afonsus1997/Pixels-Camp-PCB-Badge/Blog Writeup/Pictures/chargingcircuit.png

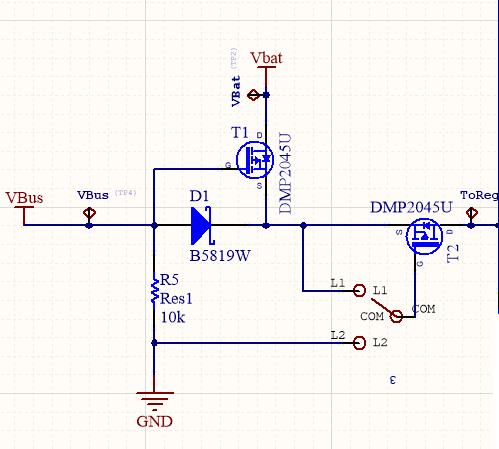
Blog Writeup/Pictures/chargingcircuit.png
