afonsus1997/Pixels-Camp-PCB-Badge/Blog Writeup/Pictures/chargingsilkscreen.PNG

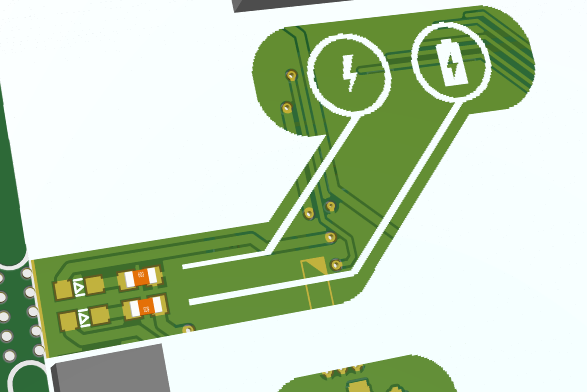
Blog Writeup/Pictures/chargingsilkscreen.PNG
