afonsus1997/Pixels-Camp-PCB-Badge/Blog Writeup/Pictures/devboard.jpg

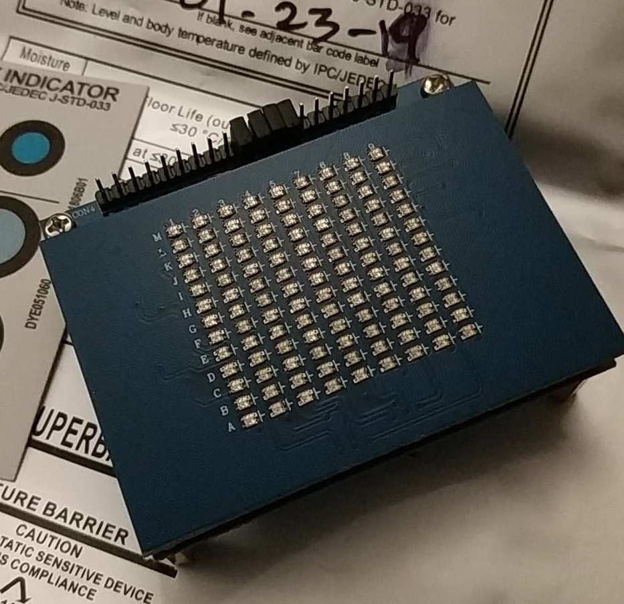
Blog Writeup/Pictures/devboard.jpg
