afonsus1997/Pixels-Camp-PCB-Badge/Blog Writeup/Pictures/DTRRST.PNG

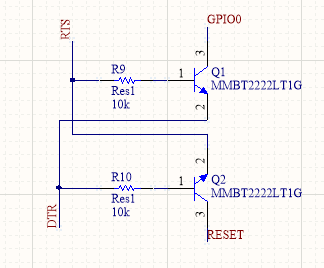
Blog Writeup/Pictures/DTRRST.PNG
