afonsus1997/Pixels-Camp-PCB-Badge/Blog Writeup/Pictures/esp32-wroom.jpg

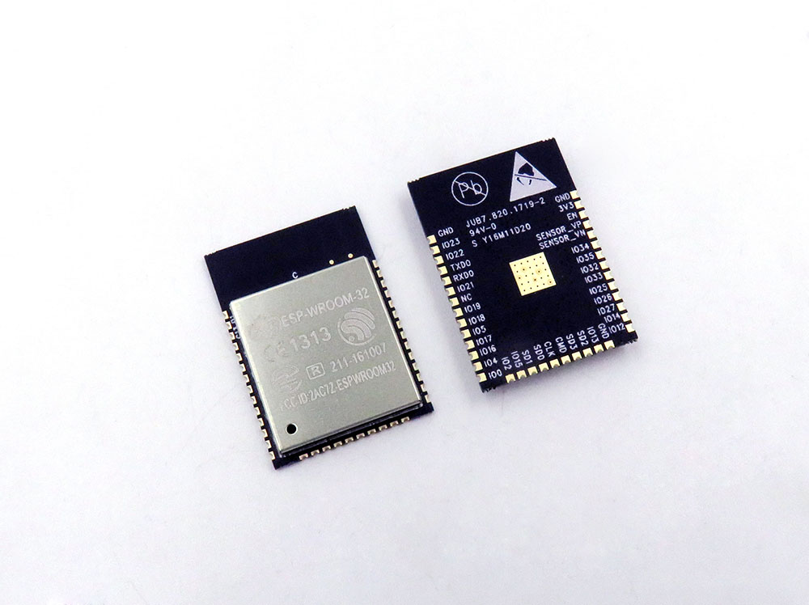
Blog Writeup/Pictures/esp32-wroom.jpg
