afonsus1997/Pixels-Camp-PCB-Badge/Blog Writeup/Pictures/esp32_pullup.PNG

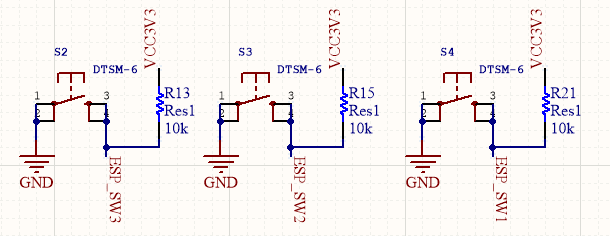
Blog Writeup/Pictures/esp32_pullup.PNG
