afonsus1997/Pixels-Camp-PCB-Badge/Blog Writeup/Pictures/Ledmatrix_pcb.PNG

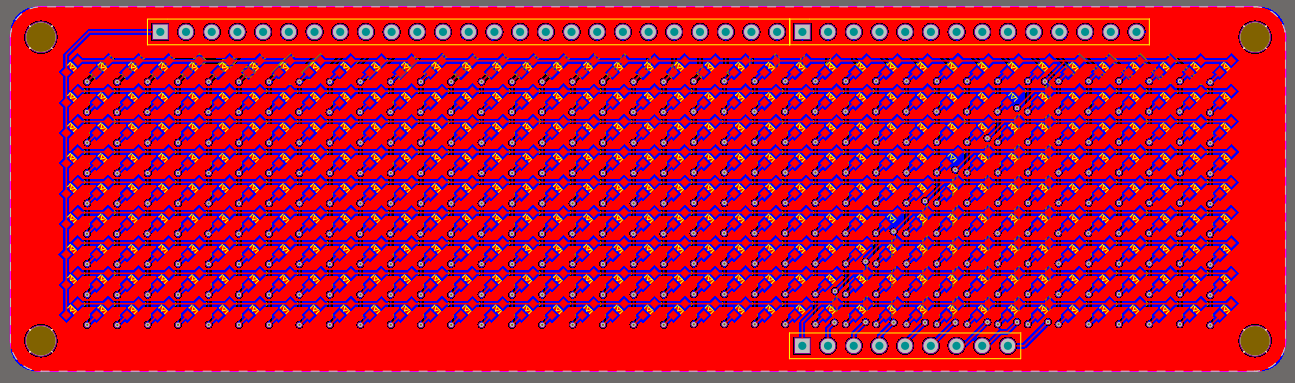
Blog Writeup/Pictures/Ledmatrix_pcb.PNG
