afonsus1997/Pixels-Camp-PCB-Badge/Blog Writeup/Pictures/panelpcb.PNG

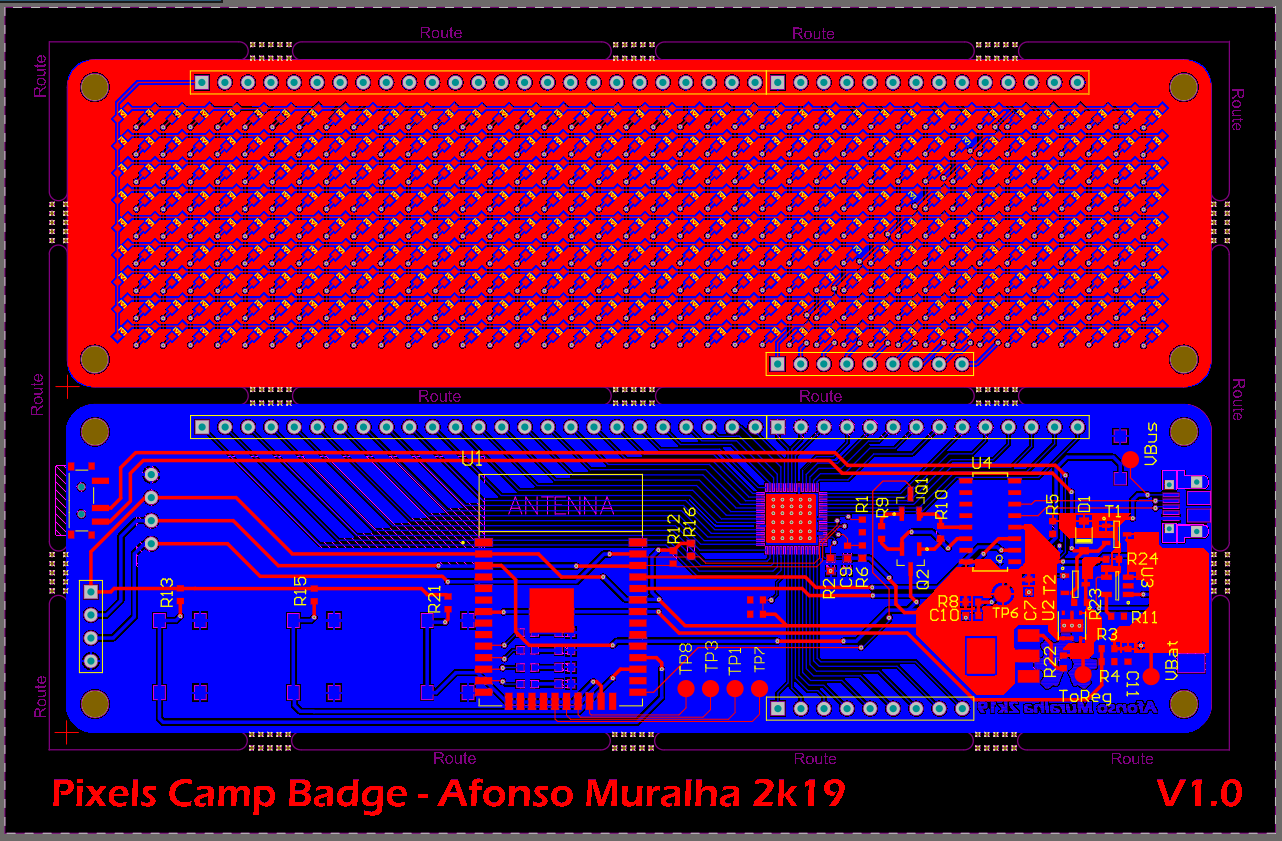
Blog Writeup/Pictures/panelpcb.PNG
