afonsus1997/Pixels-Camp-PCB-Badge/Blog Writeup/Pictures/website.PNG

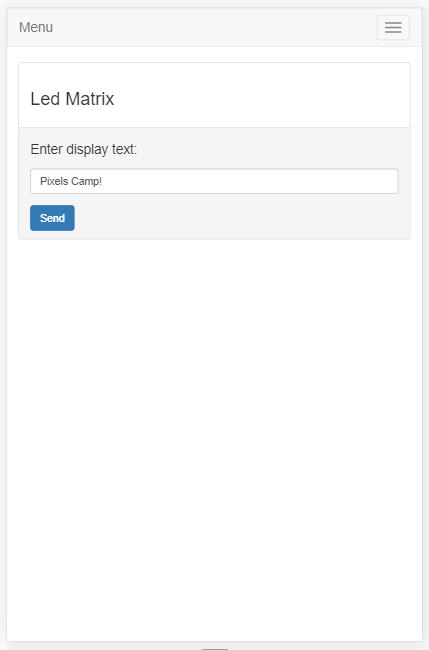
Blog Writeup/Pictures/website.PNG
