afonsus1997/Pixels-Camp-PCB-Badge/PCB ESP32/Media/Control/bot_silk.jpg

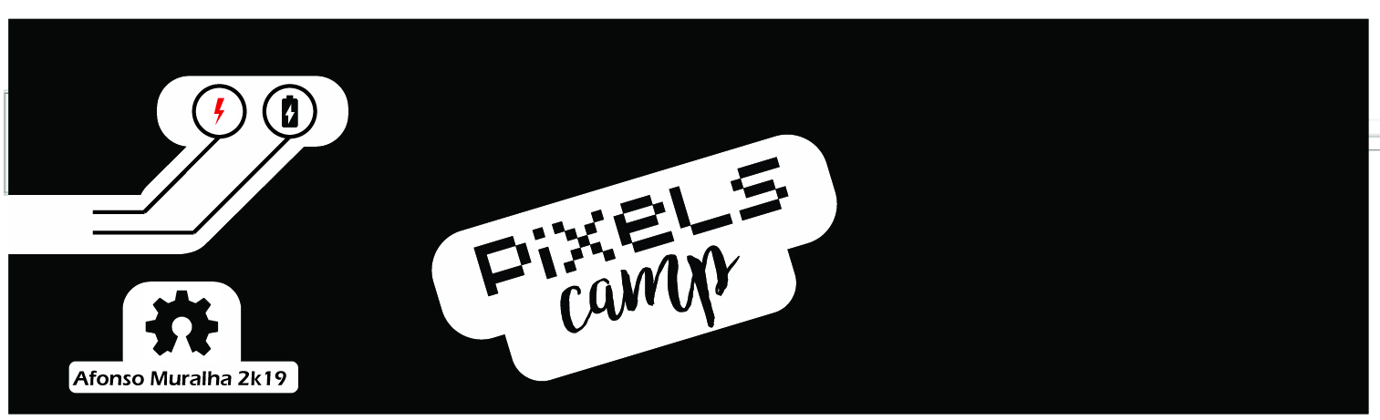
PCB ESP32/Media/Control/bot_silk.jpg
