afonsus1997/Pixels-Camp-PCB-Badge/PCB ESP32/Media/Control/bot_silkV2.jpg

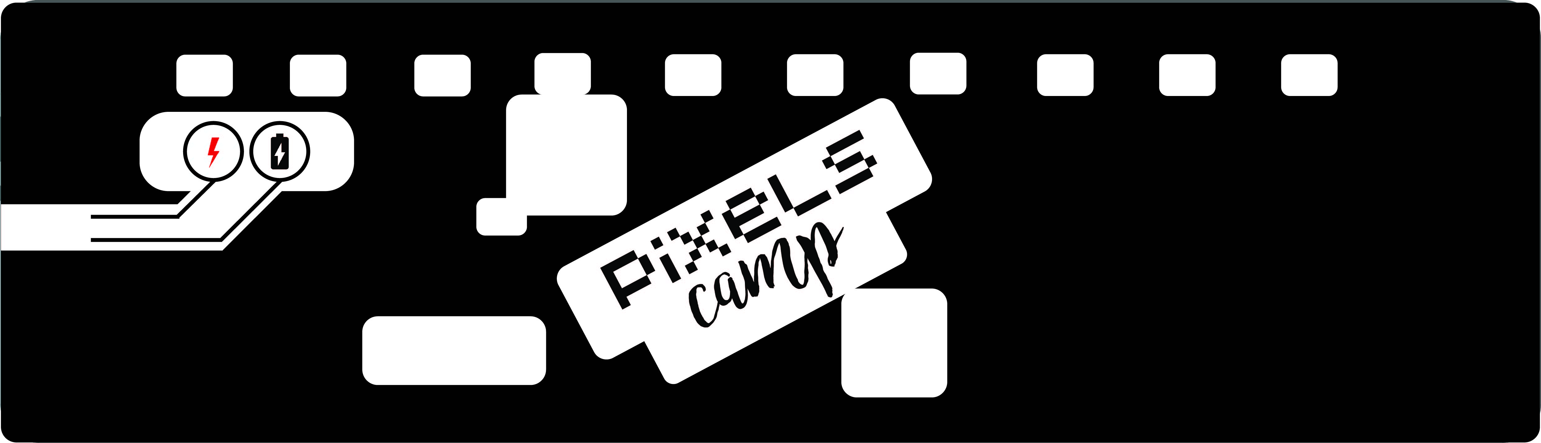
PCB ESP32/Media/Control/bot_silkV2.jpg
