afonsus1997/Pixels-Camp-PCB-Badge/PCB ESP32/Media/Control/bot_silkV2_2.png

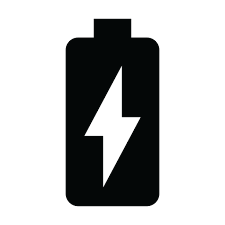
PCB ESP32/Media/Control/bot_silkV2_2.png
