afonsus1997/Pixels-Camp-PCB-Badge/PCB ESP32/Media/Control/bot_silkV2bw.bmp

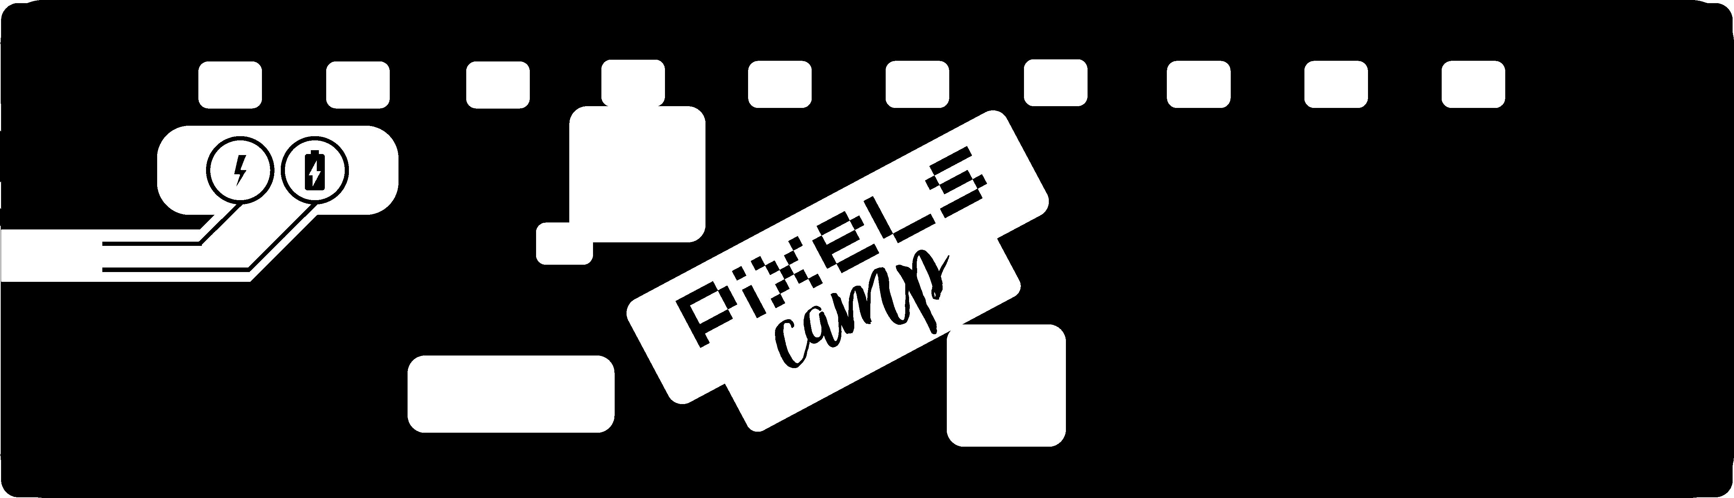
PCB ESP32/Media/Control/bot_silkV2bw.bmp
