afonsus1997/Pixels-Camp-PCB-Badge/PCB ESP32/Media/Control/PCBway1_1-ConvertImage.bmp

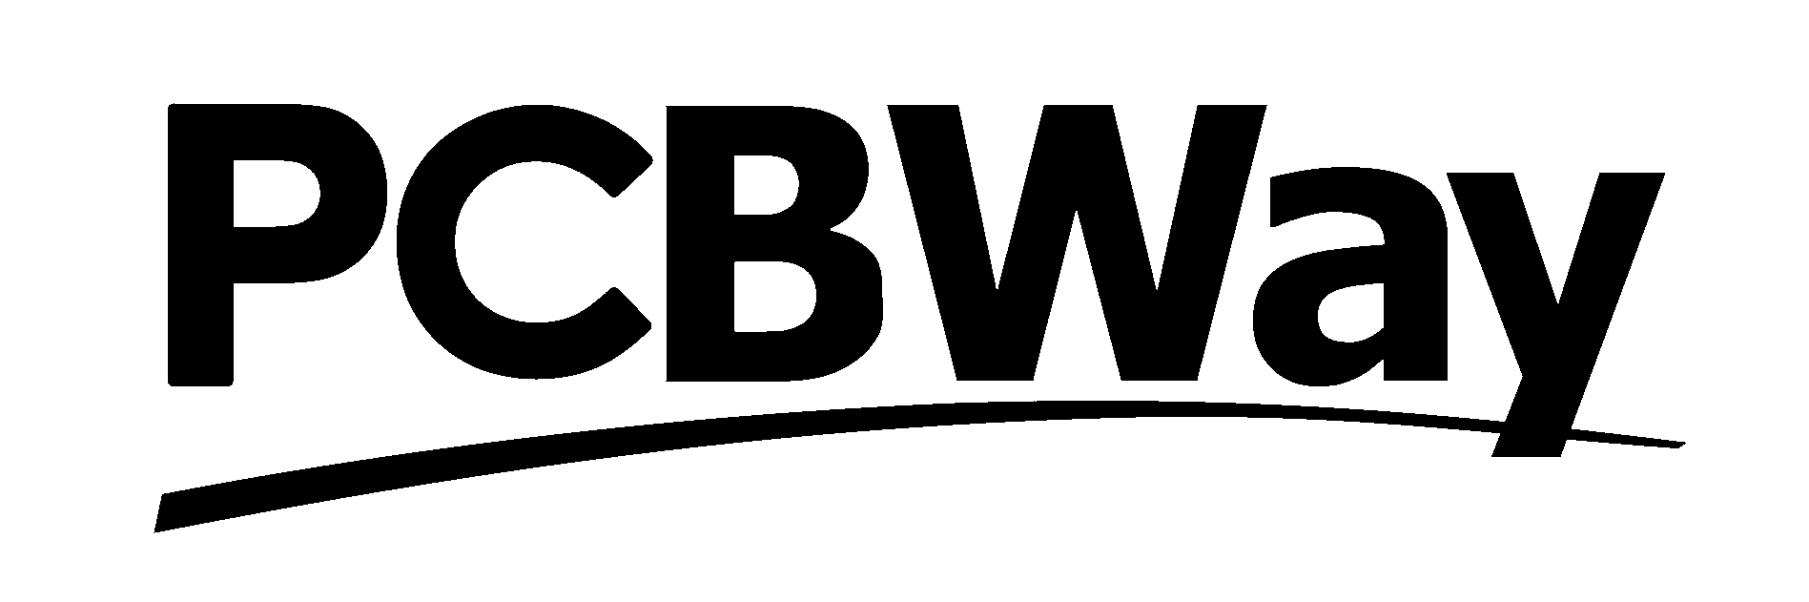
PCB ESP32/Media/Control/PCBway1_1-ConvertImage.bmp
