afonsus1997/Pixels-Camp-PCB-Badge/PCB ESP32/refs/HTB14se.KVXXXXa6aXXXq6xXFXXXI.jpg

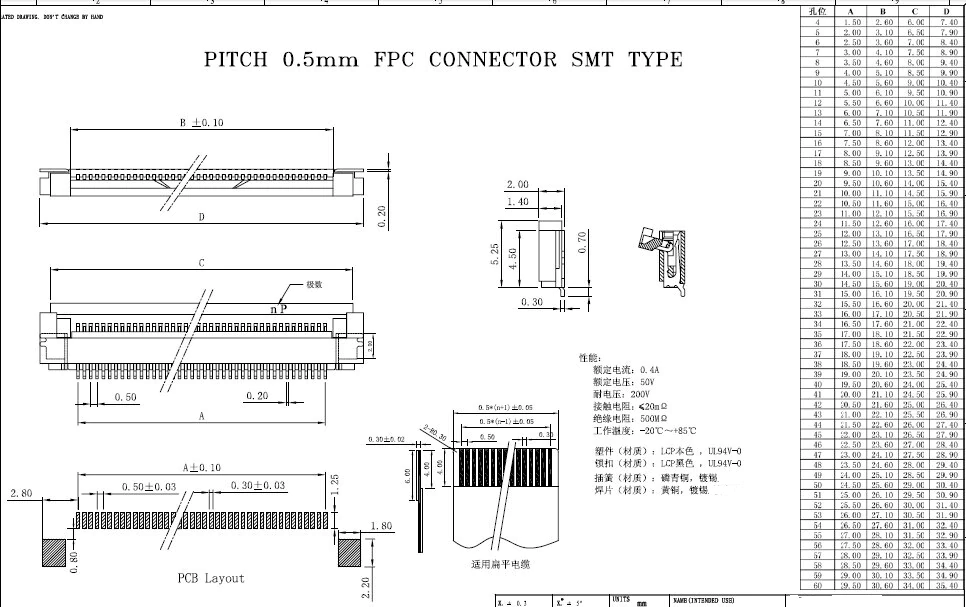
PCB ESP32/refs/HTB14se.KVXXXXa6aXXXq6xXFXXXI.jpg
