afonsus1997/Pixels-Camp-PCB-Badge/PCB ESP32/Media/Control/bot_silkV2.pdf

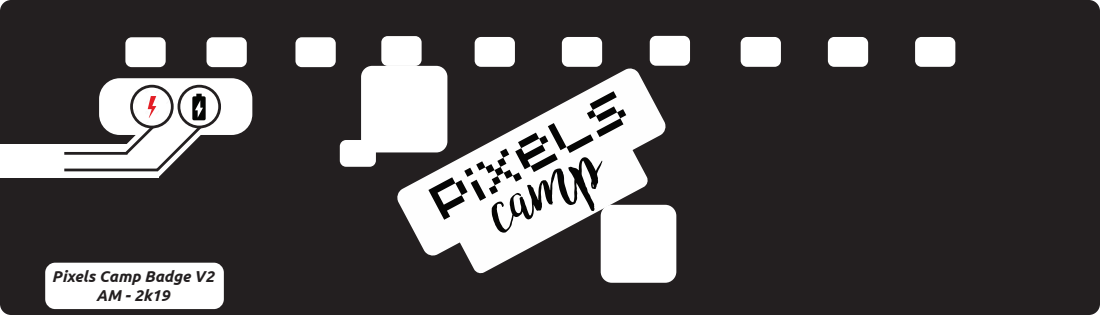
[picture p43: page 1]

Pixels Camp Badge V2
