afonsus1997/Pixels-Camp-PCB-Badge/PCB ESP32/GERBERS/Matrix/paste.pdf

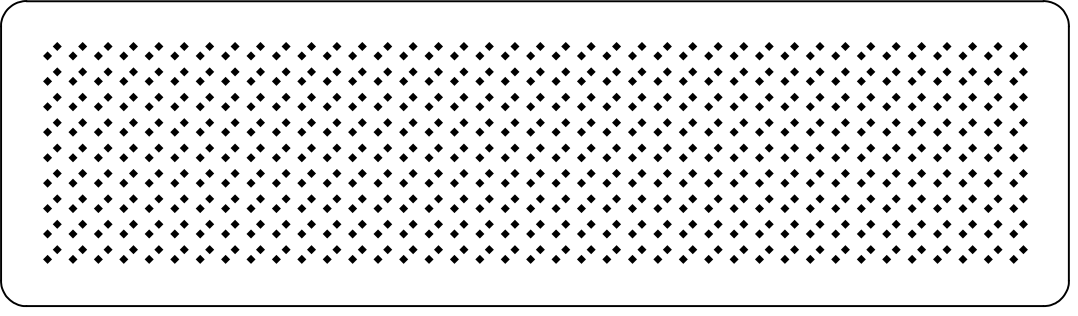
[picture p44: page 1]
