afonsus1997/Pixels-Camp-PCB-Badge/PCB ESP32/PDF/MATRIX/Job1.PDF

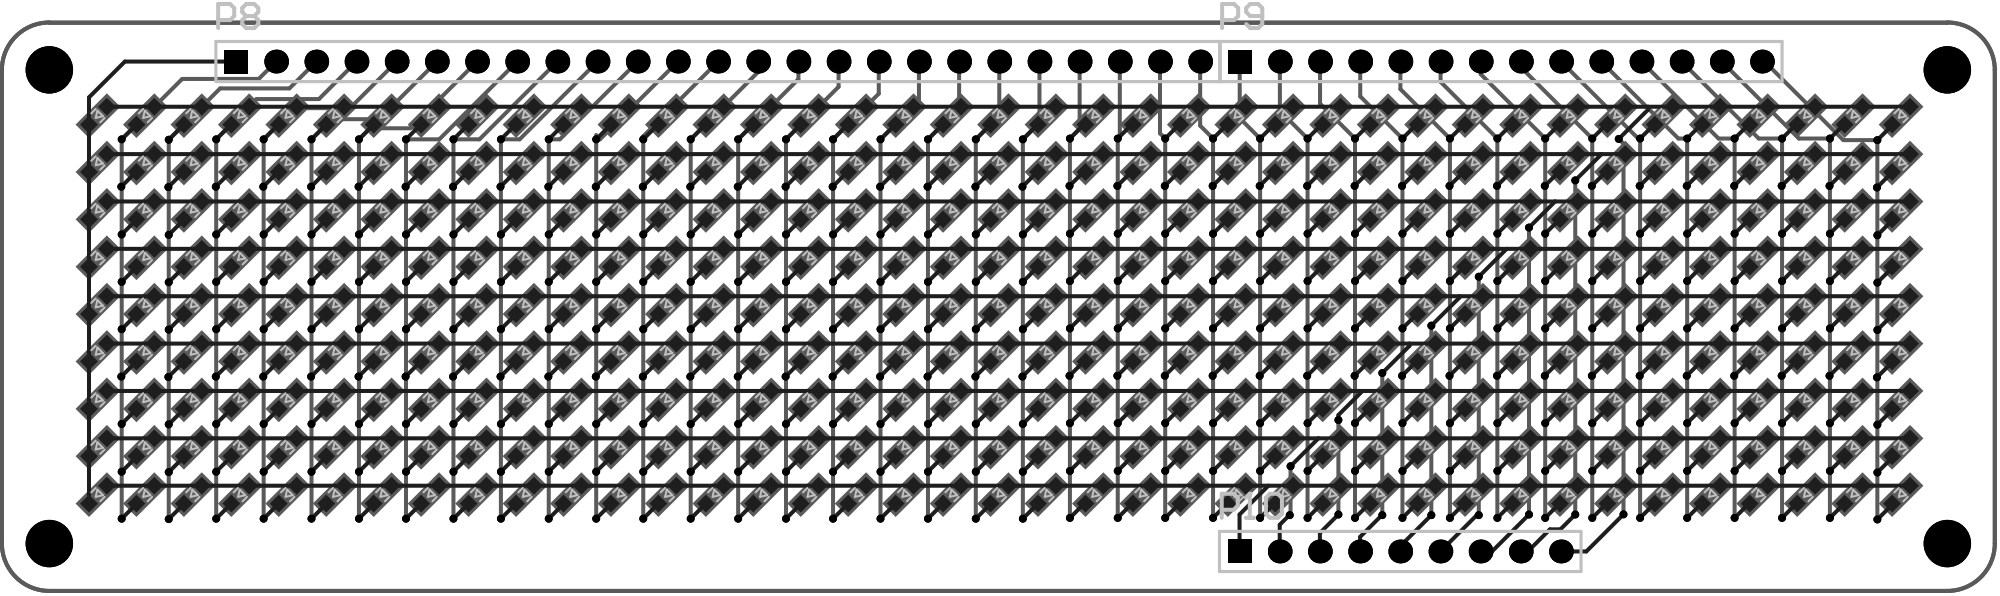
[picture p45: page 1]

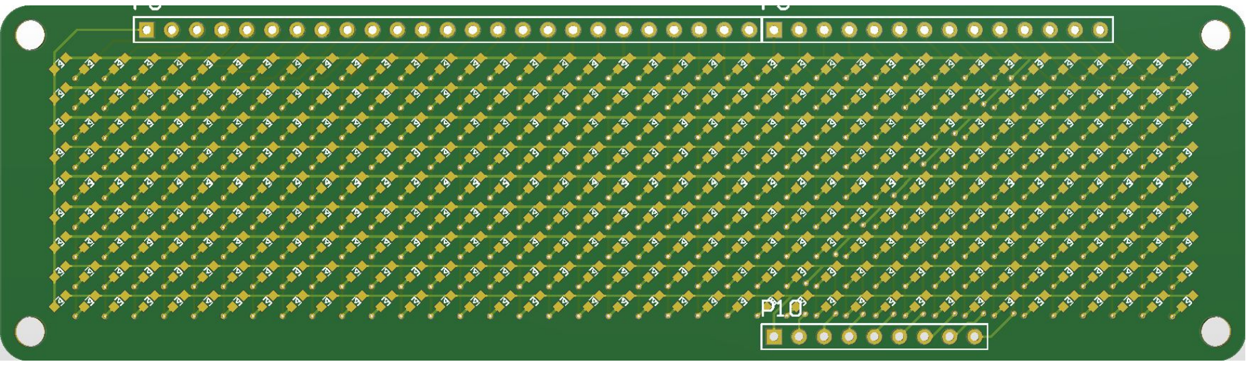
[picture p46: page 2]
