afonsus1997/Pixels-Camp-PCB-Badge/PCB ESP32/Simulations/PowerSupplySwitching.asc

D1: diode
M1: pmos; Si9433DY
M2: pmos; Si9433DY
R1: res; 10k
R2: res; 10k
U1: LT1086-3.3
V1: voltage; 0
V2: voltage; 3.7
Named nets: 0
.op
