afonsus1997/Pixels-Camp-PCB-Badge/PCB ESP32/refs/OnOnfre_DevBoard_rev4.sch

## EAGLE design PCB ESP32/refs/OnOnfre_DevBoard_rev4.sch (2019-01-10)

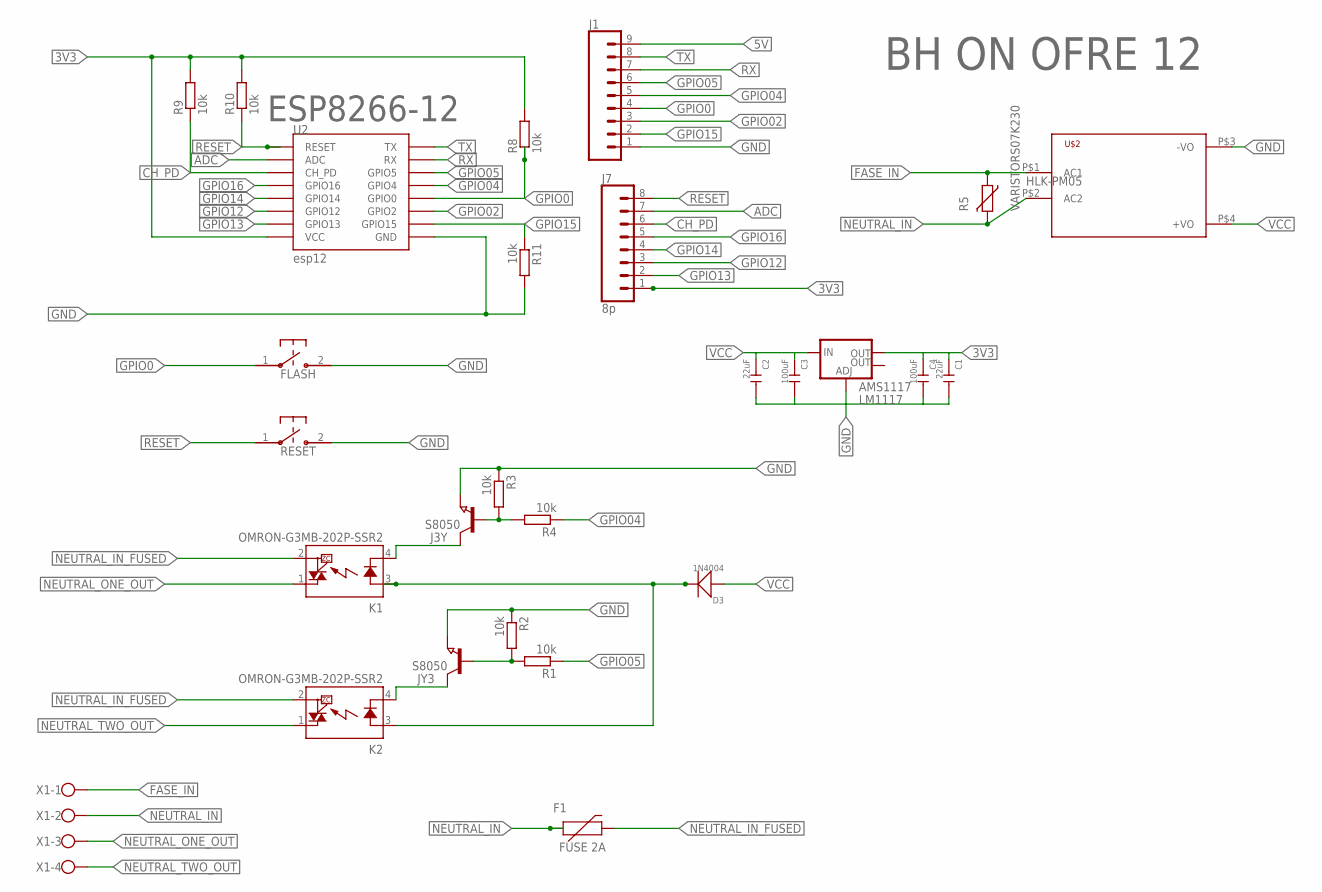
[picture p47: schematic OnOnfre_DevBoard_rev4.sch]

Parts:
AMS1117: LM1117; SOT223
C1, C2: 22uF; C1206
C3, C4: 100uF; C1206
D3: 1N4004; DO-214AC
F1: FUSE 2A; PTH
FLASH: B3U-1000P-2P-SMD; B3U-1000P
J1: CONN_09; 1X09
J3Y: S8050; SOT23
J7: 8p; 1X08
JY3: S8050; SOT23
K1, K2: OMRON-G3MB-202P-SSR2; OMRON-G3MB-202P-SSR
R1, R2, R3, R4, R8, R9, R10, R11: 10k; R0603
R5: VARISTORS07K230; S07K230
RESET: B3U-1000P-2P-SMD; B3U-1000P
U2: esp12; ESP12-SMD
U$2: HKLPM01
X1: W237-4

Connections:
3V3: AMS1117.2 (OUT), C1.1, C4.1, J7.1, R8.2, R9.2, R10.2, U2.VCC
5V: D3.2 (-), J1.9, K1.3 (A), K2.3 (A)
ADC: J7.7, U2.ADC
CH_PD: J7.6, R9.1, U2.CH_PD
FASE_IN: R5.1, U$2.P$1 (AC1), X1.1
GND: AMS1117.1 (ADJ), C1.2, C2.2, C3.2, C4.2, FLASH.2, J1.1, J3Y.2 (E), JY3.2 (E), R2.1, R3.1, R11.2, RESET.2, U2.GND, U$2.P$3 (-VO)
GPIO0: FLASH.1, J1.4, R8.1, U2.GPIO0
GPIO02: J1.3, U2.GPIO2
GPIO04: J1.5, R4.1, U2.GPIO4
GPIO05: J1.6, R1.1, U2.GPIO5
GPIO12: J7.3, U2.GPIO12
GPIO13: J7.2, U2.GPIO13
GPIO14: J7.4, U2.GPIO14
GPIO15: J1.2, R11.1, U2.GPIO15
GPIO16: J7.5, U2.GPIO16
unnamed: J3Y.3 (C), K1.4 (K)
unnamed: J3Y.1 (B), R3.2, R4.2
unnamed: JY3.3 (C), K2.4 (K)
unnamed: JY3.1 (B), R1.2, R2.2
NEUTRAL_IN: F1.P$1 (1), R5.2, U$2.P$2 (AC2), X1.2
NEUTRAL_IN_FUSED: F1.P$2 (2), K1.2 (DS2), K2.2 (DS2)
NEUTRAL_ONE_OUT: K1.1 (DS1), X1.3
NEUTRAL_TWO_OUT: K2.1 (DS1), X1.4
RESET: J7.8, R10.1, RESET.1, U2.RESET
RX: J1.7, U2.RXD0 (RX)
TX: J1.8, U2.TXD0 (TX)
VCC: AMS1117.3 (IN), C2.1, C3.1, D3.1 (+), U$2.P$4 (+VO)

Notes on the sheet:
HLK-PM05
BH ON OFRE 12
ESP8266-12
