afonsus1997/Pixels-Camp-PCB-Badge/CODE/Firmware/include/boardpins.h

#ifndef BOARDPINS_H
#define BOARDPINS_H
#define LOW 0
#define HIGH 1

#define LED1 25
#define LED2 26
#define LED3 27
#define LED4 32

#define MATRIX_EN 18
#define MATRIX_SDA 23
#define MATRIX_SCL 22
#define MATRIX_ADDR_GND 0x30



#define SWLEFT 33
#define SWCENTER 16
#define SWRIGHT 17

#define BATPIN 35

#endif
