afonsus1997/Pixels-Camp-PCB-Badge/CODE/Firmware/include/customFonts.h

const uint8_t FreeMonoOblique9pt7bBitmaps[] PROGMEM = {
  0x00, 0x11, 0x32, 0x22, 0x20, 0x04, 0xC0, 0x6D, 0xB4, 0xD2, 0x48, 0x08,
  0x0A, 0x0A, 0x02, 0x7F, 0x14, 0x04, 0xFE, 0x28, 0x28, 0x08, 0x40, 0x00,
  0x04, 0x1E, 0x21, 0x20, 0x20, 0x0E, 0x02, 0x00, 0x02, 0xBC, 0x10, 0x10,
  0x00, 0x18, 0x24, 0x24, 0x24, 0x11, 0x0C, 0x60, 0x0E, 0x12, 0x02, 0x14,
  0x1E, 0x00, 0x80, 0x03, 0x0A, 0x23, 0x44, 0x56, 0xFB, 0x68, 0x01, 0x24,
  0x4C, 0x88, 0x88, 0x88, 0x40, 0x00, 0x84, 0x20, 0x8C, 0x42, 0x11, 0x08,
  0x88, 0x00, 0x10, 0x40, 0x1E, 0x31, 0x48, 0x00, 0x00, 0x00, 0x08, 0x08,
  0x08, 0x00, 0x10, 0x10, 0x31, 0x98, 0x88, 0x40, 0x00, 0xFC, 0x00, 0x80,
  0x00, 0x40, 0x40, 0x00, 0x20, 0x20, 0x00, 0x10, 0x10, 0x10, 0x08, 0x08,
  0x00, 0x1C, 0x45, 0x08, 0x18, 0x30, 0x60, 0xC0, 0x85, 0x13, 0x40, 0x04,
  0x68, 0x00, 0x00, 0x81, 0x02, 0x00, 0x10, 0x23, 0xF8, 0x07, 0x08, 0x40,
  0x20, 0x10, 0x10, 0x10, 0x10, 0x10, 0x10, 0x20, 0x9F, 0xC0, 0x0E, 0x21,
  0x01, 0x01, 0x02, 0x0C, 0x02, 0x00, 0x00, 0x82, 0x6C, 0x03, 0x04, 0x0A,
  0x02, 0x12, 0x22, 0x40, 0x7E, 0x04, 0x04, 0x1E, 0x1F, 0x00, 0x20, 0x20,
  0x3E, 0x00, 0x01, 0x01, 0x02, 0x82, 0x6C, 0x07, 0x10, 0x20, 0x40, 0x40,
  0x24, 0xC2, 0x82, 0x80, 0x84, 0x68, 0xFF, 0x00, 0x10, 0x00, 0x80, 0x04,
  0x00, 0x20, 0x81, 0x00, 0x1C, 0x45, 0x0A, 0x14, 0x47, 0x01, 0x42, 0x04,
  0x0B, 0x60, 0x0E, 0x11, 0x20, 0x20, 0x21, 0x23, 0x1D, 0x00, 0x02, 0x04,
  0x18, 0x77, 0x00, 0x0E, 0xE0, 0x1C, 0x60, 0x00, 0x38, 0xC6, 0x10, 0xC2,
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
  {   334,  10,  10,  11,    1,   -9 },   // 0x46 'F'
  {   347,   9,  10,  11,    2,   -9 },   // 0x47 'G'
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

const GFXfont FreeMonoOblique9pt7b PROGMEM = {
  (uint8_t  *)FreeMonoOblique9pt7bBitmaps,
  (GFXglyph *)FreeMonoOblique9pt7bGlyphs,
  0x20, 0x7E, 24 };

// Approx. 1607 bytes
