afonsus1997/Pixels-Camp-PCB-Badge/CODE/ISSI Code/IS31FL3741 EVB Code V02A/IS31FL3741.c

#include "stm32f10x.h"
#include "main.h"
#include<stdlib.h>

extern volatile u8 Mode_NO;

unsigned char RGB_32PWM_IS31FL3741[144]=
{
	0X00,0X00,0X00,0X00,0X00,0X00,0X00,0X00,
	0X00,0X00,0X00,0X00,0X00,0X00,0X00,0X00,
	0X03,0x07,0x0D,0x16,0x1F,0x2E,0x40,0x4f,
	0X64,0x77,0x8D,0xA7,0xBF,0xD6,0xF1,0xFF,
	0XFF,0xF1,0xD6,0xBF,0xA7,0x8D,0x77,0X64,
	0x4f,0x40,0x2E,0x1F,0x16,0x0D,0x07,0X03,
	0X00,0X00,0X00,0X00,0X00,0X00,0X00,0X00,
	0X00,0X00,0X00,0X00,0X00,0X00,0X00,0X00,
	0X03,0x07,0x0D,0x16,0x1F,0x2E,0x40,0x4f,
	0X64,0x77,0x8D,0xA7,0xBF,0xD6,0xF1,0xFF,
	0XFF,0xF1,0xD6,0xBF,0xA7,0x8D,0x77,0X64,
	0x4f,0x40,0x2E,0x1F,0x16,0x0D,0x07,0X03,
	0X00,0X00,0X00,0X00,0X00,0X00,0X00,0X00,
	0X00,0X00,0X00,0X00,0X00,0X00,0X00,0X00,
	0X03,0x07,0x0D,0x16,0x1F,0x2E,0x40,0x4f,
	0X64,0x77,0x8D,0xA7,0xBF,0xD6,0xF1,0xFF,
	0XFF,0xF1,0xD6,0xBF,0xA7,0x8D,0x77,0X64,
	0x4f,0x40,0x2E,0x1F,0x16,0x0D,0x07,0X03,
};

u8 RGB_PWM_IS31FL3741[512]=
{
	0x00,0x01,0x02,0x03,0x04,0x05,0x06,0x07,
	0x08,0x09,0x0b,0x0d,0x0f,0x11,0x13,0x16,
	0x1a,0x1c,0x1d,0x1f,0x22,0x25,0x28,0x2e,
	0x34,0x38,0x3c,0x40,0x44,0x48,0x4b,0x4f,
	0x55,0x5a,0x5f,0x64,0x69,0x6d,0x72,0x77,
	0x7d,0x80,0x88,0x8d,0x94,0x9a,0xa0,0xa7,
	0xac,0xb0,0xb9,0xbf,0xc6,0xcb,0xcf,0xd6,
	0xe1,0xe9,0xed,0xf1,0xf6,0xfa,0xfe,0xff,

	0xff,0xfe,0xfa,0xf6,0xf1,0xed,0xe9,0xe1,
	0xd6,0xcf,0xcb,0xc6,0xbf,0xb9,0xb0,0xac,
	0xa7,0xa0,0x9a,0x94,0x8d,0x88,0x80,0x7d,
	0x77,0x72,0x6d,0x69,0x64,0x5f,0x5a,0x55,
	0x4f,0x4b,0x48,0x44,0x40,0x3c,0x38,0x34,
	0x2e,0x28,0x25,0x22,0x1f,0x1d,0x1c,0x1a,
	0x16,0x13,0x11,0x0f,0x0d,0x0b,0x09,0x08,
	0x07,0x06,0x05,0x04,0x03,0x02,0x01,0x00,
	
	0,0,0,0,0,0,0,0,
	0,0,0,0,0,0,0,0,
	0,0,0,0,0,0,0,0,
	0,0,0,0,0,0,0,0,
	0,0,0,0,0,0,0,0,
	0,0,0,0,0,0,0,0,
	0,0,0,0,0,0,0,0,
	0,0,0,0,0,0,0,0,

	0x00,0x01,0x02,0x03,0x04,0x05,0x06,0x07,
	0x08,0x09,0x0b,0x0d,0x0f,0x11,0x13,0x16,
	0x1a,0x1c,0x1d,0x1f,0x22,0x25,0x28,0x2e,
	0x34,0x38,0x3c,0x40,0x44,0x48,0x4b,0x4f,
	0x55,0x5a,0x5f,0x64,0x69,0x6d,0x72,0x77,
	0x7d,0x80,0x88,0x8d,0x94,0x9a,0xa0,0xa7,
	0xac,0xb0,0xb9,0xbf,0xc6,0xcb,0xcf,0xd6,
	0xe1,0xe9,0xed,0xf1,0xf6,0xfa,0xfe,0xff,

	0xff,0xfe,0xfa,0xf6,0xf1,0xed,0xe9,0xe1,
	0xd6,0xcf,0xcb,0xc6,0xbf,0xb9,0xb0,0xac,
	0xa7,0xa0,0x9a,0x94,0x8d,0x88,0x80,0x7d,
	0x77,0x72,0x6d,0x69,0x64,0x5f,0x5a,0x55,
	0x4f,0x4b,0x48,0x44,0x40,0x3c,0x38,0x34,
	0x2e,0x28,0x25,0x22,0x1f,0x1d,0x1c,0x1a,
	0x16,0x13,0x11,0x0f,0x0d,0x0b,0x09,0x08,
	0x07,0x06,0x05,0x04,0x03,0x02,0x01,0x00,
	
	0,0,0,0,0,0,0,0,
	0,0,0,0,0,0,0,0,
	0,0,0,0,0,0,0,0,
	0,0,0,0,0,0,0,0,
	0,0,0,0,0,0,0,0,
	0,0,0,0,0,0,0,0,
	0,0,0,0,0,0,0,0,
	0,0,0,0,0,0,0,0,

	0x00,0x01,0x02,0x03,0x04,0x05,0x06,0x07,
	0x08,0x09,0x0b,0x0d,0x0f,0x11,0x13,0x16,
	0x1a,0x1c,0x1d,0x1f,0x22,0x25,0x28,0x2e,
	0x34,0x38,0x3c,0x40,0x44,0x48,0x4b,0x4f,
	0x55,0x5a,0x5f,0x64,0x69,0x6d,0x72,0x77,
	0x7d,0x80,0x88,0x8d,0x94,0x9a,0xa0,0xa7,
	0xac,0xb0,0xb9,0xbf,0xc6,0xcb,0xcf,0xd6,
	0xe1,0xe9,0xed,0xf1,0xf6,0xfa,0xfe,0xff,

	0xff,0xfe,0xfa,0xf6,0xf1,0xed,0xe9,0xe1,
	0xd6,0xcf,0xcb,0xc6,0xbf,0xb9,0xb0,0xac,
	0xa7,0xa0,0x9a,0x94,0x8d,0x88,0x80,0x7d,
	0x77,0x72,0x6d,0x69,0x64,0x5f,0x5a,0x55,
	0x4f,0x4b,0x48,0x44,0x40,0x3c,0x38,0x34,
	0x2e,0x28,0x25,0x22,0x1f,0x1d,0x1c,0x1a,
	0x16,0x13,0x11,0x0f,0x0d,0x0b,0x09,0x08,
	0x07,0x06,0x05,0x04,0x03,0x02,0x01,0x00
};

void IS31FL3741_PWM_Write(u8 iColor, u8 iX, u8 iY, u8 idata)
{
	switch(iColor)
	{
		case R_LED: switch(iX)
								{
									case 1 :switch(iY)
													{
														case 1:I2C_WriteByte(Addr_GND_GND,0xFE,0xC5);I2C_WriteByte(Addr_GND_GND,0xFD,0x00);I2C_WriteByte(Addr_GND_GND,0x02,idata);break;
														case 2:I2C_WriteByte(Addr_GND_GND,0xFE,0xC5);I2C_WriteByte(Addr_GND_GND,0xFD,0x00);I2C_WriteByte(Addr_GND_GND,0x05,idata);break;
														case 3:I2C_WriteByte(Addr_GND_GND,0xFE,0xC5);I2C_WriteByte(Addr_GND_GND,0xFD,0x00);I2C_WriteByte(Addr_GND_GND,0x08,idata);break;
														case 4:I2C_WriteByte(Addr_GND_GND,0xFE,0xC5);I2C_WriteByte(Addr_GND_GND,0xFD,0x00);I2C_WriteByte(Addr_GND_GND,0x0B,idata);break;
														case 5:I2C_WriteByte(Addr_GND_GND,0xFE,0xC5);I2C_WriteByte(Addr_GND_GND,0xFD,0x00);I2C_WriteByte(Addr_GND_GND,0x0E,idata);break;
														case 6:I2C_WriteByte(Addr_GND_GND,0xFE,0xC5);I2C_WriteByte(Addr_GND_GND,0xFD,0x00);I2C_WriteByte(Addr_GND_GND,0x11,idata);break;
														case 7:I2C_WriteByte(Addr_GND_GND,0xFE,0xC5);I2C_WriteByte(Addr_GND_GND,0xFD,0x00);I2C_WriteByte(Addr_GND_GND,0x14,idata);break;
														case 8:I2C_WriteByte(Addr_GND_GND,0xFE,0xC5);I2C_WriteByte(Addr_GND_GND,0xFD,0x00);I2C_WriteByte(Addr_GND_GND,0x17,idata);break;
														case 9:I2C_WriteByte(Addr_GND_GND,0xFE,0xC5);I2C_WriteByte(Addr_GND_GND,0xFD,0x00);I2C_WriteByte(Addr_GND_GND,0x1A,idata);break;
														case 10:I2C_WriteByte(Addr_GND_GND,0xFE,0xC5);I2C_WriteByte(Addr_GND_GND,0xFD,0x00);I2C_WriteByte(Addr_GND_GND,0x1D,idata);break;
														case 11:I2C_WriteByte(Addr_GND_GND,0xFE,0xC5);I2C_WriteByte(Addr_GND_GND,0xFD,0x01);I2C_WriteByte(Addr_GND_GND,0x5C,idata);break;
														case 12:I2C_WriteByte(Addr_GND_GND,0xFE,0xC5);I2C_WriteByte(Addr_GND_GND,0xFD,0x01);I2C_WriteByte(Addr_GND_GND,0x5F,idata);break;
														case 13:I2C_WriteByte(Addr_GND_GND,0xFE,0xC5);I2C_WriteByte(Addr_GND_GND,0xFD,0x01);I2C_WriteByte(Addr_GND_GND,0x62,idata);break;
														default: break;
													}break;
									case 2 :switch(iY)
													{
														case 1:I2C_WriteByte(Addr_GND_GND,0xFE,0xC5);I2C_WriteByte(Addr_GND_GND,0xFD,0x00);I2C_WriteByte(Addr_GND_GND,0x20,idata);break;
														case 2:I2C_WriteByte(Addr_GND_GND,0xFE,0xC5);I2C_WriteByte(Addr_GND_GND,0xFD,0x00);I2C_WriteByte(Addr_GND_GND,0x23,idata);break;
														case 3:I2C_WriteByte(Addr_GND_GND,0xFE,0xC5);I2C_WriteByte(Addr_GND_GND,0xFD,0x00);I2C_WriteByte(Addr_GND_GND,0x26,idata);break;
														case 4:I2C_WriteByte(Addr_GND_GND,0xFE,0xC5);I2C_WriteByte(Addr_GND_GND,0xFD,0x00);I2C_WriteByte(Addr_GND_GND,0x29,idata);break;
														case 5:I2C_WriteByte(Addr_GND_GND,0xFE,0xC5);I2C_WriteByte(Addr_GND_GND,0xFD,0x00);I2C_WriteByte(Addr_GND_GND,0x2C,idata);break;
														case 6:I2C_WriteByte(Addr_GND_GND,0xFE,0xC5);I2C_WriteByte(Addr_GND_GND,0xFD,0x00);I2C_WriteByte(Addr_GND_GND,0x2F,idata);break;
														case 7:I2C_WriteByte(Addr_GND_GND,0xFE,0xC5);I2C_WriteByte(Addr_GND_GND,0xFD,0x00);I2C_WriteByte(Addr_GND_GND,0x32,idata);break;
														case 8:I2C_WriteByte(Addr_GND_GND,0xFE,0xC5);I2C_WriteByte(Addr_GND_GND,0xFD,0x00);I2C_WriteByte(Addr_GND_GND,0x35,idata);break;
														case 9:I2C_WriteByte(Addr_GND_GND,0xFE,0xC5);I2C_WriteByte(Addr_GND_GND,0xFD,0x00);I2C_WriteByte(Addr_GND_GND,0x38,idata);break;
														case 10:I2C_WriteByte(Addr_GND_GND,0xFE,0xC5);I2C_WriteByte(Addr_GND_GND,0xFD,0x00);I2C_WriteByte(Addr_GND_GND,0x3B,idata);break;
														case 11:I2C_WriteByte(Addr_GND_GND,0xFE,0xC5);I2C_WriteByte(Addr_GND_GND,0xFD,0x01);I2C_WriteByte(Addr_GND_GND,0x65,idata);break;
														case 12:I2C_WriteByte(Addr_GND_GND,0xFE,0xC5);I2C_WriteByte(Addr_GND_GND,0xFD,0x01);I2C_WriteByte(Addr_GND_GND,0x68,idata);break;
														case 13:I2C_WriteByte(Addr_GND_GND,0xFE,0xC5);I2C_WriteByte(Addr_GND_GND,0xFD,0x01);I2C_WriteByte(Addr_GND_GND,0x6B,idata);break;
														default: break;
													}break;
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
	IS31FL3741_R_LED_SCAL_PWM(PWM,0x00);
	IS31FL3741_G_LED_SCAL_PWM(PWM,0x00);
	IS31FL3741_B_LED_SCAL_PWM(PWM,0x00);
	
	I2C_WriteByte(Addr_GND_GND,0xfe,0xc5);
	I2C_WriteByte(Addr_GND_GND,0xfD,0x04);
	I2C_WriteByte(Addr_GND_GND,0x01,0xFF);//GCC
	I2C_WriteByte(Addr_GND_GND,0x00,0x01);
}

u8 IS31FL3741_Mode_1(void)//Rainbow wave
{
	u8 com1;
	u8 x=128;
	u8 y=64;
	u8 z=8;
	
	IS31FL3741_R_LED_SCAL_PWM(PWM,0x00);
	IS31FL3741_G_LED_SCAL_PWM(PWM,0x00);
	IS31FL3741_B_LED_SCAL_PWM(PWM,0x00);
	
	while(Mode_NO == 1)
	{
		for(com1=0;com1<189;com1++)
		{	
			IS31FL3741_LED_Y_Samedata(G_LED,1,RGB_PWM_IS31FL3741[com1]);
			IS31FL3741_LED_Y_Samedata(R_LED,1,RGB_PWM_IS31FL3741[com1+x]);
			IS31FL3741_LED_Y_Samedata(B_LED,1,RGB_PWM_IS31FL3741[com1+y]);
	
			IS31FL3741_LED_Y_Samedata(G_LED,2,RGB_PWM_IS31FL3741[com1+z*1]);
			IS31FL3741_LED_Y_Samedata(R_LED,2,RGB_PWM_IS31FL3741[com1+x+z*1]);
			IS31FL3741_LED_Y_Samedata(B_LED,2,RGB_PWM_IS31FL3741[com1+y+z*1]);
	
			IS31FL3741_LED_Y_Samedata(G_LED,3,RGB_PWM_IS31FL3741[com1+z*2]);
			IS31FL3741_LED_Y_Samedata(R_LED,3,RGB_PWM_IS31FL3741[com1+x+z*2]);
			IS31FL3741_LED_Y_Samedata(B_LED,3,RGB_PWM_IS31FL3741[com1+y+z*2]);
		
			IS31FL3741_LED_Y_Samedata(G_LED,4,RGB_PWM_IS31FL3741[com1+z*3]);
			IS31FL3741_LED_Y_Samedata(R_LED,4,RGB_PWM_IS31FL3741[com1+x+z*3]);
			IS31FL3741_LED_Y_Samedata(B_LED,4,RGB_PWM_IS31FL3741[com1+y+z*3]);
			
			IS31FL3741_LED_Y_Samedata(G_LED,5,RGB_PWM_IS31FL3741[com1+z*4]);
			IS31FL3741_LED_Y_Samedata(R_LED,5,RGB_PWM_IS31FL3741[com1+x+z*4]);
			IS31FL3741_LED_Y_Samedata(B_LED,5,RGB_PWM_IS31FL3741[com1+y+z*4]);
			
			IS31FL3741_LED_Y_Samedata(G_LED,6,RGB_PWM_IS31FL3741[com1+z*5]);
			IS31FL3741_LED_Y_Samedata(R_LED,6,RGB_PWM_IS31FL3741[com1+x+z*5]);
			IS31FL3741_LED_Y_Samedata(B_LED,6,RGB_PWM_IS31FL3741[com1+y+z*5]);
			
			IS31FL3741_LED_Y_Samedata(G_LED,7,RGB_PWM_IS31FL3741[com1+z*6]);
			IS31FL3741_LED_Y_Samedata(R_LED,7,RGB_PWM_IS31FL3741[com1+x+z*6]);
			IS31FL3741_LED_Y_Samedata(B_LED,7,RGB_PWM_IS31FL3741[com1+y+z*6]);
			
			IS31FL3741_LED_Y_Samedata(G_LED,8,RGB_PWM_IS31FL3741[com1+z*7]);
			IS31FL3741_LED_Y_Samedata(R_LED,8,RGB_PWM_IS31FL3741[com1+x+z*7]);
			IS31FL3741_LED_Y_Samedata(B_LED,8,RGB_PWM_IS31FL3741[com1+y+z*7]);
			
			IS31FL3741_LED_Y_Samedata(G_LED,9,RGB_PWM_IS31FL3741[com1+z*8]);
			IS31FL3741_LED_Y_Samedata(R_LED,9,RGB_PWM_IS31FL3741[com1+x+z*8]);
			IS31FL3741_LED_Y_Samedata(B_LED,9,RGB_PWM_IS31FL3741[com1+y+z*8]);
			
			IS31FL3741_LED_Y_Samedata(G_LED,10,RGB_PWM_IS31FL3741[com1+z*9]);
			IS31FL3741_LED_Y_Samedata(R_LED,10,RGB_PWM_IS31FL3741[com1+x+z*9]);
			IS31FL3741_LED_Y_Samedata(B_LED,10,RGB_PWM_IS31FL3741[com1+y+z*9]);
			
			IS31FL3741_LED_Y_Samedata(G_LED,11,RGB_PWM_IS31FL3741[com1+z*10]);
			IS31FL3741_LED_Y_Samedata(R_LED,11,RGB_PWM_IS31FL3741[com1+x+z*10]);
			IS31FL3741_LED_Y_Samedata(B_LED,11,RGB_PWM_IS31FL3741[com1+y+z*10]);
			
			IS31FL3741_LED_Y_Samedata(G_LED,12,RGB_PWM_IS31FL3741[com1+z*11]);
			IS31FL3741_LED_Y_Samedata(R_LED,12,RGB_PWM_IS31FL3741[com1+x+z*11]);
			IS31FL3741_LED_Y_Samedata(B_LED,12,RGB_PWM_IS31FL3741[com1+y+z*11]);
			
			IS31FL3741_LED_Y_Samedata(G_LED,13,RGB_PWM_IS31FL3741[com1+z*12]);
			IS31FL3741_LED_Y_Samedata(R_LED,13,RGB_PWM_IS31FL3741[com1+x+z*12]);
			IS31FL3741_LED_Y_Samedata(B_LED,13,RGB_PWM_IS31FL3741[com1+y+z*12]);
			if(Mode_NO != 1)return 0;
		}	
	}
	return 1;
}

u8 IS31FL3741_Mode_2(void)//Rainbow wave
{
	u8 i;
	u8 p_temp;
	u8 pb1,pr1,pg1;
	pb1 = 0;
	pr1 = 16;
	pg1 = 32;
	IS31FL3741_R_LED_SCAL_PWM(PWM,0x00);
	IS31FL3741_G_LED_SCAL_PWM(PWM,0x00);
	IS31FL3741_B_LED_SCAL_PWM(PWM,0x00);
	while(Mode_NO == 2)
	{
		for(i=0;i<48;i++)
		{
			p_temp=i+pr1;
				IS31FL3741_LED_Y(R_LED,1,RGB_32PWM_IS31FL3741[24+p_temp],RGB_32PWM_IS31FL3741[21+p_temp],RGB_32PWM_IS31FL3741[18+p_temp],RGB_32PWM_IS31FL3741[15+p_temp],RGB_32PWM_IS31FL3741[12+p_temp],RGB_32PWM_IS31FL3741[9+p_temp],RGB_32PWM_IS31FL3741[6+p_temp],RGB_32PWM_IS31FL3741[3+p_temp],RGB_32PWM_IS31FL3741[0+p_temp]);
				p_temp=i+pb1;
				IS31FL3741_LED_Y(B_LED,1,RGB_32PWM_IS31FL3741[24+p_temp],RGB_32PWM_IS31FL3741[21+p_temp],RGB_32PWM_IS31FL3741[18+p_temp],RGB_32PWM_IS31FL3741[15+p_temp],RGB_32PWM_IS31FL3741[12+p_temp],RGB_32PWM_IS31FL3741[9+p_temp],RGB_32PWM_IS31FL3741[6+p_temp],RGB_32PWM_IS31FL3741[3+p_temp],RGB_32PWM_IS31FL3741[0+p_temp]);
				p_temp=i+pg1;
				IS31FL3741_LED_Y(G_LED,1,RGB_32PWM_IS31FL3741[24+p_temp],RGB_32PWM_IS31FL3741[21+p_temp],RGB_32PWM_IS31FL3741[18+p_temp],RGB_32PWM_IS31FL3741[15+p_temp],RGB_32PWM_IS31FL3741[12+p_temp],RGB_32PWM_IS31FL3741[9+p_temp],RGB_32PWM_IS31FL3741[6+p_temp],RGB_32PWM_IS31FL3741[3+p_temp],RGB_32PWM_IS31FL3741[0+p_temp]);
				p_temp=i+pr1+2;
				IS31FL3741_LED_Y(R_LED,2,RGB_32PWM_IS31FL3741[24+p_temp],RGB_32PWM_IS31FL3741[21+p_temp],RGB_32PWM_IS31FL3741[18+p_temp],RGB_32PWM_IS31FL3741[15+p_temp],RGB_32PWM_IS31FL3741[12+p_temp],RGB_32PWM_IS31FL3741[9+p_temp],RGB_32PWM_IS31FL3741[6+p_temp],RGB_32PWM_IS31FL3741[3+p_temp],RGB_32PWM_IS31FL3741[0+p_temp]);
				p_temp=i+pb1+2;
				IS31FL3741_LED_Y(B_LED,2,RGB_32PWM_IS31FL3741[24+p_temp],RGB_32PWM_IS31FL3741[21+p_temp],RGB_32PWM_IS31FL3741[18+p_temp],RGB_32PWM_IS31FL3741[15+p_temp],RGB_32PWM_IS31FL3741[12+p_temp],RGB_32PWM_IS31FL3741[9+p_temp],RGB_32PWM_IS31FL3741[6+p_temp],RGB_32PWM_IS31FL3741[3+p_temp],RGB_32PWM_IS31FL3741[0+p_temp]);
				p_temp=i+pg1+2;
				IS31FL3741_LED_Y(G_LED,2,RGB_32PWM_IS31FL3741[24+p_temp],RGB_32PWM_IS31FL3741[21+p_temp],RGB_32PWM_IS31FL3741[18+p_temp],RGB_32PWM_IS31FL3741[15+p_temp],RGB_32PWM_IS31FL3741[12+p_temp],RGB_32PWM_IS31FL3741[9+p_temp],RGB_32PWM_IS31FL3741[6+p_temp],RGB_32PWM_IS31FL3741[3+p_temp],RGB_32PWM_IS31FL3741[0+p_temp]);
				p_temp=i+pr1+4;
				IS31FL3741_LED_Y(R_LED,3,RGB_32PWM_IS31FL3741[24+p_temp],RGB_32PWM_IS31FL3741[21+p_temp],RGB_32PWM_IS31FL3741[18+p_temp],RGB_32PWM_IS31FL3741[15+p_temp],RGB_32PWM_IS31FL3741[12+p_temp],RGB_32PWM_IS31FL3741[9+p_temp],RGB_32PWM_IS31FL3741[6+p_temp],RGB_32PWM_IS31FL3741[3+p_temp],RGB_32PWM_IS31FL3741[0+p_temp]);
				p_temp=i+pb1+4;
				IS31FL3741_LED_Y(B_LED,3,RGB_32PWM_IS31FL3741[24+p_temp],RGB_32PWM_IS31FL3741[21+p_temp],RGB_32PWM_IS31FL3741[18+p_temp],RGB_32PWM_IS31FL3741[15+p_temp],RGB_32PWM_IS31FL3741[12+p_temp],RGB_32PWM_IS31FL3741[9+p_temp],RGB_32PWM_IS31FL3741[6+p_temp],RGB_32PWM_IS31FL3741[3+p_temp],RGB_32PWM_IS31FL3741[0+p_temp]);
				p_temp=i+pg1+4;
				IS31FL3741_LED_Y(G_LED,3,RGB_32PWM_IS31FL3741[24+p_temp],RGB_32PWM_IS31FL3741[21+p_temp],RGB_32PWM_IS31FL3741[18+p_temp],RGB_32PWM_IS31FL3741[15+p_temp],RGB_32PWM_IS31FL3741[12+p_temp],RGB_32PWM_IS31FL3741[9+p_temp],RGB_32PWM_IS31FL3741[6+p_temp],RGB_32PWM_IS31FL3741[3+p_temp],RGB_32PWM_IS31FL3741[0+p_temp]);
				p_temp=i+pr1+6;
				IS31FL3741_LED_Y(R_LED,4,RGB_32PWM_IS31FL3741[24+p_temp],RGB_32PWM_IS31FL3741[21+p_temp],RGB_32PWM_IS31FL3741[18+p_temp],RGB_32PWM_IS31FL3741[15+p_temp],RGB_32PWM_IS31FL3741[12+p_temp],RGB_32PWM_IS31FL3741[9+p_temp],RGB_32PWM_IS31FL3741[6+p_temp],RGB_32PWM_IS31FL3741[3+p_temp],RGB_32PWM_IS31FL3741[0+p_temp]);
				p_temp=i+pb1+6;
				IS31FL3741_LED_Y(B_LED,4,RGB_32PWM_IS31FL3741[24+p_temp],RGB_32PWM_IS31FL3741[21+p_temp],RGB_32PWM_IS31FL3741[18+p_temp],RGB_32PWM_IS31FL3741[15+p_temp],RGB_32PWM_IS31FL3741[12+p_temp],RGB_32PWM_IS31FL3741[9+p_temp],RGB_32PWM_IS31FL3741[6+p_temp],RGB_32PWM_IS31FL3741[3+p_temp],RGB_32PWM_IS31FL3741[0+p_temp]);
				p_temp=i+pg1+6;
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
				p_temp=i+pg1+20;
				IS31FL3741_LED_Y(G_LED,11,RGB_32PWM_IS31FL3741[24+p_temp],RGB_32PWM_IS31FL3741[21+p_temp],RGB_32PWM_IS31FL3741[18+p_temp],RGB_32PWM_IS31FL3741[15+p_temp],RGB_32PWM_IS31FL3741[12+p_temp],RGB_32PWM_IS31FL3741[9+p_temp],RGB_32PWM_IS31FL3741[6+p_temp],RGB_32PWM_IS31FL3741[3+p_temp],RGB_32PWM_IS31FL3741[0+p_temp]);
				p_temp=i+pr1+22;
				IS31FL3741_LED_Y(R_LED,12,RGB_32PWM_IS31FL3741[24+p_temp],RGB_32PWM_IS31FL3741[21+p_temp],RGB_32PWM_IS31FL3741[18+p_temp],RGB_32PWM_IS31FL3741[15+p_temp],RGB_32PWM_IS31FL3741[12+p_temp],RGB_32PWM_IS31FL3741[9+p_temp],RGB_32PWM_IS31FL3741[6+p_temp],RGB_32PWM_IS31FL3741[3+p_temp],RGB_32PWM_IS31FL3741[0+p_temp]);
				p_temp=i+pb1+22;
				IS31FL3741_LED_Y(B_LED,12,RGB_32PWM_IS31FL3741[24+p_temp],RGB_32PWM_IS31FL3741[21+p_temp],RGB_32PWM_IS31FL3741[18+p_temp],RGB_32PWM_IS31FL3741[15+p_temp],RGB_32PWM_IS31FL3741[12+p_temp],RGB_32PWM_IS31FL3741[9+p_temp],RGB_32PWM_IS31FL3741[6+p_temp],RGB_32PWM_IS31FL3741[3+p_temp],RGB_32PWM_IS31FL3741[0+p_temp]);
				p_temp=i+pg1+22;
				IS31FL3741_LED_Y(G_LED,12,RGB_32PWM_IS31FL3741[24+p_temp],RGB_32PWM_IS31FL3741[21+p_temp],RGB_32PWM_IS31FL3741[18+p_temp],RGB_32PWM_IS31FL3741[15+p_temp],RGB_32PWM_IS31FL3741[12+p_temp],RGB_32PWM_IS31FL3741[9+p_temp],RGB_32PWM_IS31FL3741[6+p_temp],RGB_32PWM_IS31FL3741[3+p_temp],RGB_32PWM_IS31FL3741[0+p_temp]);
				p_temp=i+pr1+24;
				IS31FL3741_LED_Y(R_LED,13,RGB_32PWM_IS31FL3741[24+p_temp],RGB_32PWM_IS31FL3741[21+p_temp],RGB_32PWM_IS31FL3741[18+p_temp],RGB_32PWM_IS31FL3741[15+p_temp],RGB_32PWM_IS31FL3741[12+p_temp],RGB_32PWM_IS31FL3741[9+p_temp],RGB_32PWM_IS31FL3741[6+p_temp],RGB_32PWM_IS31FL3741[3+p_temp],RGB_32PWM_IS31FL3741[0+p_temp]);
				p_temp=i+pb1+24;
				IS31FL3741_LED_Y(B_LED,13,RGB_32PWM_IS31FL3741[24+p_temp],RGB_32PWM_IS31FL3741[21+p_temp],RGB_32PWM_IS31FL3741[18+p_temp],RGB_32PWM_IS31FL3741[15+p_temp],RGB_32PWM_IS31FL3741[12+p_temp],RGB_32PWM_IS31FL3741[9+p_temp],RGB_32PWM_IS31FL3741[6+p_temp],RGB_32PWM_IS31FL3741[3+p_temp],RGB_32PWM_IS31FL3741[0+p_temp]);
				p_temp=i+pg1+24;
				IS31FL3741_LED_Y(G_LED,13,RGB_32PWM_IS31FL3741[24+p_temp],RGB_32PWM_IS31FL3741[21+p_temp],RGB_32PWM_IS31FL3741[18+p_temp],RGB_32PWM_IS31FL3741[15+p_temp],RGB_32PWM_IS31FL3741[12+p_temp],RGB_32PWM_IS31FL3741[9+p_temp],RGB_32PWM_IS31FL3741[6+p_temp],RGB_32PWM_IS31FL3741[3+p_temp],RGB_32PWM_IS31FL3741[0+p_temp]);
				if (Mode_NO != 2) return 0;
				delay_ms(100);
				
		}
	}
	return 1;
}

u8 IS31FL3741_Mode_3(void)//Rain
{
	u8 iCnt = 0;
	u8 x,y,k;
	u8 irand = rand()%9;
	u8 R_PWM = rand()%256;
	u8 G_PWM = rand()%256;
	u8 B_PWM = rand()%256;
	u8 ColorPWM[9][13][3];
	IS31FL3741_R_LED_SCAL_PWM(PWM,0x00);
	IS31FL3741_G_LED_SCAL_PWM(PWM,0x00);
	IS31FL3741_B_LED_SCAL_PWM(PWM,0x00);
	for (y=0;y<13;y++)//Init table
	{
		for (x=0;x<9;x++)
		{
			for(k=0;k<3;k++)
			{
				ColorPWM[x][y][k] = 0x00;
			}
		}
	}
	
	while(Mode_NO == 3)
	{
			
		if (iCnt == 3)
		{
			iCnt = 0;
			irand = rand()%9;//Get random numbers 
			R_PWM = rand()%256;
			G_PWM = rand()%256;
			B_PWM = rand()%256;
		}
		if(Mode_NO != 3)return 0;
		for (x=0;x<9;x++)//data transformation
		{
			if (irand == x)
			{
				if (iCnt == 0)
				{
					ColorPWM[x][12][0] = R_PWM;
					ColorPWM[x][12][1] = G_PWM;
					ColorPWM[x][12][2] = B_PWM;
				}
				else
				{
					if (iCnt == 1)
					{
						ColorPWM[x][12][0] = R_PWM/2;
						ColorPWM[x][12][1] = G_PWM/2;
						ColorPWM[x][12][2] = B_PWM/2;
					}
					else
					if(iCnt == 2)
					{
						ColorPWM[x][12][0] = R_PWM/8;
						ColorPWM[x][12][1] = G_PWM/8;
						ColorPWM[x][12][2] = B_PWM/8;
					}
					else
					{
						ColorPWM[x][12][0] = 0x00;
						ColorPWM[x][12][1] = 0x00;
						ColorPWM[x][12][2] = 0x00;
					}
				}				
			}
			else
			{
				ColorPWM[x][12][0] = 0x00;
				ColorPWM[x][12][1] = 0x00;
				ColorPWM[x][12][2] = 0x00;
			}		
		}
		iCnt++;
		for (x=0;x<9;x++)//update LED data
		{
			for (y=0;y<13;y++)
			{
				IS31FL3741_PWM_Write(R_LED,x+1,y+1,ColorPWM[x][y][0]);
				IS31FL3741_PWM_Write(G_LED,x+1,y+1,ColorPWM[x][y][1]);
				IS31FL3741_PWM_Write(B_LED,x+1,y+1,ColorPWM[x][y][2]);
				if(Mode_NO != 3)return 0;
			}
		}
		delay_ms(100);
		if(Mode_NO != 3)return 0;
		for (x=0;x<9;x++)//Data downward movement 
		{
			for (y=0;y<12;y++)
			{
				for (k=0;k<3;k++)
				{
					ColorPWM[x][y][k] = ColorPWM[x][y+1][k];
				}
			}
		}
		
	}
	return 1;
}

u8 IS31FL3741_Mode_4(void)//Visor
{
	u8 iCnt = 0;
	u8 x,y,k;

	u8 R_PWM = rand()%256;
	u8 G_PWM = rand()%256;
	u8 B_PWM = rand()%256;
	u8 ColorPWM[9][13][3];
	IS31FL3741_R_LED_SCAL_PWM(PWM,0x00);
	IS31FL3741_G_LED_SCAL_PWM(PWM,0x00);
	IS31FL3741_B_LED_SCAL_PWM(PWM,0x00);
	for (y=0;y<13;y++)//Init table
	{
		for (x=0;x<9;x++)
		{
			for(k=0;k<3;k++)
			{
				ColorPWM[x][y][k] = 0x00;
			}
		}
	}
	
	while(Mode_NO == 4)
	{
		for(iCnt=0;iCnt<15;iCnt++)
		{
			if (iCnt == 14)
			{
				R_PWM = rand()%256;
				G_PWM = rand()%256;
				B_PWM = rand()%256;
			}
			if(Mode_NO != 4)return 0;	
			for (y=0;y<13;y++)//data transformation
			{
				if (iCnt == 0)
				{
					ColorPWM[0][y][0] = R_PWM;
					ColorPWM[0][y][1] = G_PWM;
					ColorPWM[0][y][2] = B_PWM;
				}
				else
				{
					if (iCnt == 1)
					{
						ColorPWM[0][y][0] = R_PWM/2;
						ColorPWM[0][y][1] = G_PWM/2;
						ColorPWM[0][y][2] = B_PWM/2;
					}
					else
					if(iCnt == 2)
					{
						ColorPWM[0][y][0] = R_PWM/3;
						ColorPWM[0][y][1] = G_PWM/3;
						ColorPWM[0][y][2] = B_PWM/3;
					}
					else
					if(iCnt == 3)
					{
						ColorPWM[0][y][0] = R_PWM/4;
						ColorPWM[0][y][1] = G_PWM/4;
						ColorPWM[0][y][2] = B_PWM/4;
					}
					else
					if(iCnt == 4)
					{
						ColorPWM[0][y][0] = R_PWM/6;
						ColorPWM[0][y][1] = G_PWM/6;
						ColorPWM[0][y][2] = B_PWM/6;
					}
					else
					if(iCnt == 5)
					{
						ColorPWM[0][y][0] = R_PWM/8;
						ColorPWM[0][y][1] = G_PWM/8;
						ColorPWM[0][y][2] = B_PWM/8;
					}
					else
					{
						ColorPWM[0][y][0] = 0x00;
						ColorPWM[0][y][1] = 0x00;
						ColorPWM[0][y][2] = 0x00;
					}
				}				
			}
			for (x=0;x<9;x++)//update data
			{
				for (y=0;y<13;y++)
				{
					IS31FL3741_PWM_Write(R_LED,x+1,y+1,ColorPWM[x][y][0]);
					IS31FL3741_PWM_Write(G_LED,x+1,y+1,ColorPWM[x][y][1]);
					IS31FL3741_PWM_Write(B_LED,x+1,y+1,ColorPWM[x][y][2]);
					
				}if(Mode_NO != 4)return 0;
			}
			if(Mode_NO != 4)return 0;
			
			for(y=0;y<13;y++)//Move data right 
			{
				for (x=8;x>0;x--)
				{
					for (k=0;k<3;k++)
					{
						ColorPWM[x][y][k] = ColorPWM[x-1][y][k];
					}
				}
 			}
		}
		for(iCnt=0;iCnt<15;iCnt++)
		{
			if (iCnt == 14)
			{
				R_PWM = rand()%256;
				G_PWM = rand()%256;
				B_PWM = rand()%256;
			}
				
			for (y=0;y<13;y++)//data transformation
			{
				if (iCnt == 0)
				{
					ColorPWM[8][y][0] = R_PWM;
					ColorPWM[8][y][1] = G_PWM;
					ColorPWM[8][y][2] = B_PWM;
				}
				else
				{
					if (iCnt == 1)
					{
						ColorPWM[8][y][0] = R_PWM/2;
						ColorPWM[8][y][1] = G_PWM/2;
						ColorPWM[8][y][2] = B_PWM/2;
					}
					else
					if(iCnt == 2)
					{
						ColorPWM[8][y][0] = R_PWM/3;
						ColorPWM[8][y][1] = G_PWM/3;
						ColorPWM[8][y][2] = B_PWM/3;
					}
					else
					if(iCnt == 3)
					{
						ColorPWM[8][y][0] = R_PWM/4;
						ColorPWM[8][y][1] = G_PWM/4;
						ColorPWM[8][y][2] = B_PWM/4;
					}
					else
					if(iCnt == 4)
					{
						ColorPWM[8][y][0] = R_PWM/6;
						ColorPWM[8][y][1] = G_PWM/6;
						ColorPWM[8][y][2] = B_PWM/6;
					}
					else
					if(iCnt == 5)
					{
						ColorPWM[8][y][0] = R_PWM/8;
						ColorPWM[8][y][1] = G_PWM/8;
						ColorPWM[8][y][2] = B_PWM/8;
					}
					else
					{
						ColorPWM[8][y][0] = 0x00;
						ColorPWM[8][y][1] = 0x00;
						ColorPWM[8][y][2] = 0x00;
					}
				}				
			}
			for (x=0;x<9;x++)//update data
			{
				for (y=0;y<13;y++)
				{
					IS31FL3741_PWM_Write(R_LED,x+1,y+1,ColorPWM[x][y][0]);
					IS31FL3741_PWM_Write(G_LED,x+1,y+1,ColorPWM[x][y][1]);
					IS31FL3741_PWM_Write(B_LED,x+1,y+1,ColorPWM[x][y][2]);
					if(Mode_NO != 4)return 0;
				}
			}
			if(Mode_NO != 4)return 0;
			for (x=0;x<8;x++)//Move data left 
			{
				for (y=0;y<13;y++)
				{
					for (k=0;k<3;k++)
					{
						ColorPWM[x][y][k] = ColorPWM[x+1][y][k];
					}
				}
 			}
  	}
		delay_ms(1000);
	}
	return 1;
}

void Play_IS31FL3741_Demo_mode(void)
{
	IS31FL3741_Mode_1();
	while(Mode_NO == 1);  
	IS31FL3741_Mode_2();
	while(Mode_NO == 2);  
	IS31FL3741_Mode_3();
	while(Mode_NO == 3); 
	IS31FL3741_Mode_4();
	while(Mode_NO == 4);
}
