afonsus1997/Pixels-Camp-PCB-Badge/CODE/Firmware/include/wifip.h

#ifndef WIFIP_H
#define WIFIP_H

#include <SPIFFS.h>
#include <WiFi.h>
#include <WiFiClient.h>
#include <WiFiServer.h>
#include <WiFiUdp.h>
#include <WiFiAP.h>
#include <AsyncTCP.h>
#include "ESPAsyncWebServer.h"

#include "wifi_credentials.h"

#endif
