afonsus1997/Pixels-Camp-PCB-Badge/CODE/Firmware/src/bitmaps.h

const unsigned char glasses [] PROGMEM = {
// 'Webp, 39x9px
	0xff, 0xff, 0xff, 0xff, 0xfe, 0xff, 0xff, 0xe3, 0xff, 0xfe, 0xb3, 0xff, 0xc1, 0x37, 0xfe, 0x93, 
	0xff, 0xc1, 0x27, 0xfe, 0xcc, 0xff, 0xc1, 0xc9, 0xfe, 0x73, 0x7f, 0x80, 0xe2, 0xfc, 0x73, 0x3f, 
	0x00, 0xf6, 0x7c, 0x1f, 0xfe, 0x00, 0x3f, 0xf0, 0x1f, 0xfe, 0x00, 0x3f, 0xf0, 
	// 'Webp, 39x9px
	0xff, 0xff, 0xff, 0xff, 0xfe, 0xe4, 0xff, 0xe2, 0x4f, 0xfe, 0xe4, 0xff, 0xc2, 0x4f, 0xfe, 0x20, 
	0x3f, 0xc2, 0x03, 0xf8, 0x10, 0x1f, 0xc1, 0x81, 0xf0, 0x0c, 0x9f, 0x80, 0xc8, 0xe0, 0x04, 0x9e, 
	0x00, 0x49, 0xc0, 0x07, 0xfe, 0x00, 0x7f, 0xc0, 0x00, 0x00, 0x00, 0x00, 0x00
};

// 'pxls', 39x10px
const unsigned char pixels [] PROGMEM = {
	0x06, 0x5e, 0x81, 0xbf, 0x82, 0x7a, 0x61, 0x81, 0xbf, 0x06, 0x06, 0x6d, 0x9f, 0xbf, 0xfa, 0x7f, 
	0xde, 0xc1, 0x81, 0x06, 0xff, 0xff, 0xfd, 0xff, 0xfe, 0xff, 0x75, 0x4d, 0x07, 0xfe, 0xff, 0x62, 
	0x4b, 0x27, 0xfe, 0xff, 0x7f, 0xfa, 0x2f, 0xfe, 0xff, 0xff, 0xff, 0x3f, 0xfe, 0xff, 0xff, 0xff, 
	0xff, 0xfe
};
