afonsus1997/Pixels-Camp-PCB-Badge/CODE/ISSI Code/IS31FL3741 EVB Code V02A/IS31FL3741.h

/* Define to prevent recursive inclusion ------------------------------------ */ 
#ifndef __IS31FL3741_H 
#define __IS31FL3741_H 
#include "stm32f10x.h"

void Play_IS31FL3741_Demo_mode(void);
void IS31FL3741_Init(void);
#endif 
