afonsus1997/Pixels-Camp-PCB-Badge/CODE/uGUI_Example/uGUI v0.3/image.h

#include "ugui.h"

#ifndef _BMP
#define _BMP

const UG_U16 logo_bmp[] =
{
  0xF79E, 0xF79E, 0xF79E, 0xF79E, 0xF79E, 0xF79E, 0xF79E, 0xF79E, 0xF79E, 0xF79E, 0xF79E, 0xF79E, 0xF79E, 0xF79E, 0xF79E, 0xF79E, 0xF79E, 0xF79E, 0xF79E, 0xF79E, 0xF79E, 0xF79E, 0xF79E, 0xF79E, 0xF79E, 0xF79E, 0xF79E, 0xF79E, 0xF79E, 0xEF7D, 0xDEDB,
        0xB5B7, 0x94B3, 0x73CF, 0x6B8E, 0x5AEC, 0x52EC, 0x52CD, 0x42CD, 0x3A6E, 0x324E, 0x322D, 0x322D, 0x320D, 0x31EB, 0x426D, 0x5B30, 0x7C13, 0xA537, 0xCE9B, 0xEF7D, 0xF79E, 0xF79E, 0xF79E, 0xF79E, 0xF79E, 0xF79E, 0xF79E, 0xF79E, 0xF79E, 0xF79E,
        0xF79E, 0xF79E, 0xF79E, 0xF79E, 0xF79E, 0xF79E, 0xF79E, 0xF79E, 0xF79E, 0xF79E, 0xF79E, 0xF79E, 0xF79E, 0xF79E, 0xF79E, 0xF79E, 0xF79E, 0xF79E, 0xF79E,
  0xF79E, 0xF79E, 0xF79E, 0xF79E, 0xF79E, 0xF79E, 0xF79E, 0xF79E, 0xF79E, 0xF79E, 0xF79E, 0xF79E, 0xF79E, 0xF79E, 0xF79E, 0xF79E, 0xF79E, 0xF79E, 0xF79E, 0xF79E, 0xF79E, 0xF79E, 0xF79E, 0xF79E, 0xF79E, 0xF79E, 0xEF7D, 0xC659, 0x8CB4, 0x5B8F, 0x4B0E,
        0x3AAE, 0x3270, 0x3292, 0x3AB3, 0x3294, 0x2A75, 0x32B5, 0x2276, 0x2A56, 0x2A57, 0x3258, 0x2A38, 0x3258, 0x3258, 0x2A58, 0x2A39, 0x225A, 0x1A3A, 0x19FA, 0x3A9B, 0x743C, 0xADBC, 0xEF5D, 0xF79E, 0xF79E, 0xF79E, 0xF79E, 0xF79E, 0xF79E, 0xF79E,
        0xF79E, 0xF79E, 0xF79E, 0xF79E, 0xF79E, 0xF79E, 0xF79E, 0xF79E, 0xF79E, 0xF79E, 0xF79E, 0xF79E, 0xF79E, 0xF79E, 0xF79E, 0xF79E, 0xF79E, 0xF79E, 0xF79E,
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
        0x515B, 0x29FF, 0x035F, 0x03BF, 0x041F, 0x037F, 0x12DF, 0x0C5F, 0x867C, 0xF79E, 0xF79E, 0xF79E, 0xF79E, 0xF79E, 0xF79E, 0xF79E, 0xF79E, 0xF79E, 0xF79E,
  0xF79E, 0xF79E, 0xF79E, 0xF79E, 0xF79E, 0xF79E, 0xF79E, 0xF79E, 0xF79E, 0xCE38, 0x3985, 0x18C1, 0x20A2, 0x2082, 0x2082, 0x2883, 0x28A4, 0x28A4, 0x20C6, 0x11EE, 0x063E, 0x07FF, 0x07FF, 0x079F, 0x07FF, 0x07FF, 0x077F, 0x06BF, 0x07FF, 0x07FF, 0x041E,
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
};

const UG_BMP logo =
{
   (void*)logo_bmp,
   80,
   80,
   BMP_BPP_16,
   BMP_RGB565
};

#endif
