afonsus1997/Pixels-Camp-PCB-Badge/CODE/uGUI_Example/uGUI v0.3/system.h

// ------------------------------------
// µGUI example project
// http://www.embeddedlightning.com/
// ------------------------------------


#ifndef __SYSTEM_H
#define __SYSTEM_H

#include "stm32f4xx_conf.h"
#include "stm32f4xx.h"
#include "stdint.h"
#include "ugui.h"
#include "ltdc.h"
#include "sdram.h"
#include "ili9341.h"
#include "delay.h"
#include <stdio.h>
#include <math.h>
#include "stm32f429i_discovery_ioe.h"
#include "stm32f429i_discovery.h"
#include <stdlib.h>

extern u32 ltdc_work_layer;

#endif
